wararyo/CapsuleChord/M5Chorder/images/1.jpg

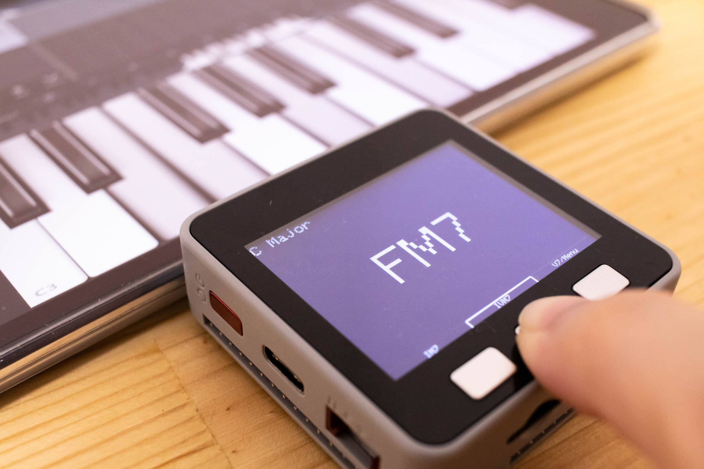
M5Chorder/images/1.jpg
