wararyo/CapsuleChord/M5Chorder/src/Context.h

#ifndef _CONTEXT_H_
#define _CONTEXT_H_

#include "Settings.h"
#include "Chord.h"

class Context {
public:
    Settings* settings;
    Scale* scale;
    void (*playChord)(Chord);
    void (*sendNotes)(bool,std::vector<uint8_t>,int);

    Context(){}
    Context(Settings* settings):settings(settings){
        scale = &((SettingItemScale*)settings->findSettingByKey(String("Scale")))->content;
    }

    static Context *getContext(){
        if(_instance == nullptr) _instance = new Context();
        return _instance;
    }
    static void setContext(Context *context) {
        _instance = context;
    }

protected:
    static Context *_instance; 
};

#endif
