wararyo/CapsuleChord/M5Chorder/src/BLEMidi.cpp

#include <BLEMidi.h>

void BLEMidi::begin(std::string deviceName,
    BLEServerCallbacks *serverCallback,
    BLECharacteristicCallbacks *characteristicCallback) {

    this->deviceName = deviceName;

    BLEDevice::init(deviceName);
    BLEDevice::setEncryptionLevel((esp_ble_sec_act_t)ESP_LE_AUTH_REQ_SC_BOND);

    //Start Server
    server = BLEDevice::createServer();
    server->setCallbacks(serverCallback);
    BLEService *service = server->createService(BLEUUID(midiServiceUUID));
    characteristic = service->createCharacteristic(
    BLEUUID(midiCharacteristicUUID),
    BLECharacteristic::PROPERTY_READ   |
    BLECharacteristic::PROPERTY_NOTIFY |
    BLECharacteristic::PROPERTY_WRITE_NR
    );
    characteristic->setAccessPermissions(ESP_GATT_PERM_READ_ENCRYPTED | ESP_GATT_PERM_WRITE_ENCRYPTED);
    characteristic->setCallbacks(characteristicCallback);
    characteristic->addDescriptor(new BLE2902());
    service->start();

    //Start Advertising
    BLEAdvertisementData advertisementData = BLEAdvertisementData();
    advertisementData.setFlags(0x04);
    advertisementData.setCompleteServices(BLEUUID(midiServiceUUID));
    advertisementData.setName(deviceName);
    advertising = server->getAdvertising();
    advertising->setAdvertisementData(advertisementData);
    advertising->addServiceUUID(MIDI_SERVICE_UUID);

    BLESecurity *security = new BLESecurity();
    security->setAuthenticationMode(ESP_LE_AUTH_REQ_SC_BOND);
    security->setCapability(ESP_IO_CAP_NONE);
    security->setInitEncryptionKey(ESP_BLE_ENC_KEY_MASK | ESP_BLE_ID_KEY_MASK);

    advertising->start();
}

void BLEMidi::sendNote(uint8_t status, uint8_t noteNo, uint8_t vel) {
    uint8_t midiPacket[] = {
        0x80,  // header
        0x80,  // timestamp, not implemented
        0x00,  // status
        0x3c,  // 0x3c == 60 == middle c
        0x00   // velocity
    };
    midiPacket[2] = status; // note on/off, channel 0
    midiPacket[3] = noteNo;
    midiPacket[4] = vel;
    characteristic->setValue(midiPacket, 5); // packet, length in bytes)
    characteristic->notify();
}

BLEMidi Midi;
